betaBison/umnitsa_robot/componentTesting/listener.py

#!/usr/bin/env python

import rospy
from std_msgs.msg import String
from umnitsa_msgs import console_controller

def callback(data):
    rospy.loginfo(rospy.get_caller_id() + 'I heard %s', data.data)

def updateCommand(data):
    rospy.loginfo(data)

def listener():

    # In ROS, nodes are uniquely named. If two nodes with the same
    # name are launched, the previous one is kicked off. The
    # anonymous=True flag means that rospy will choose a unique
    # name for our 'listener' node so that multiple listeners can
    # run simultaneously.
    rospy.init_node('listener', anonymous=True)

    rospy.Subscriber('chatter', String, callback)
    rospy.Subscriber('commands',console_controller, updateCommand)

    # spin() simply keeps python from exiting until this node is stopped
    rospy.spin()

if __name__ == '__main__':
    listener()
